RymanSatProject/hobby_sat_book/05_Schematic/esp32/2_top.png

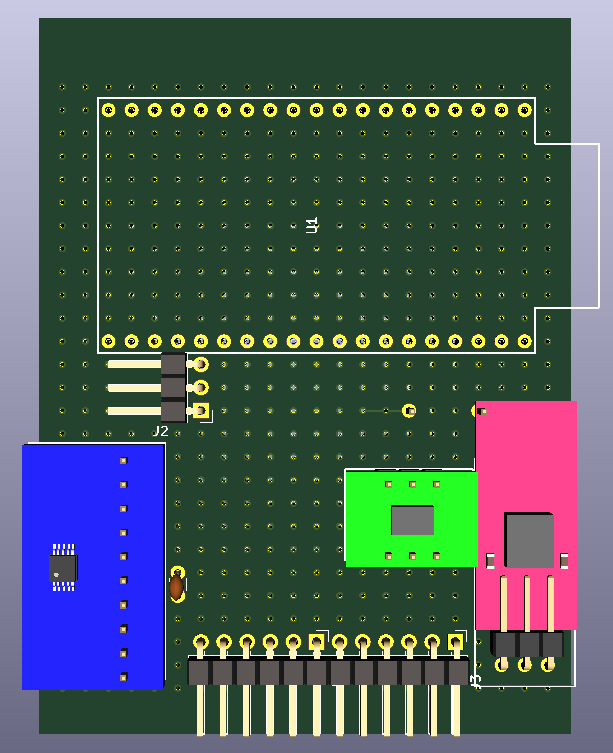
05_Schematic/esp32/2_top.png
