RymanSatProject/hobby_sat_book/05_Schematic/RaspberryPi/3_top.jpg

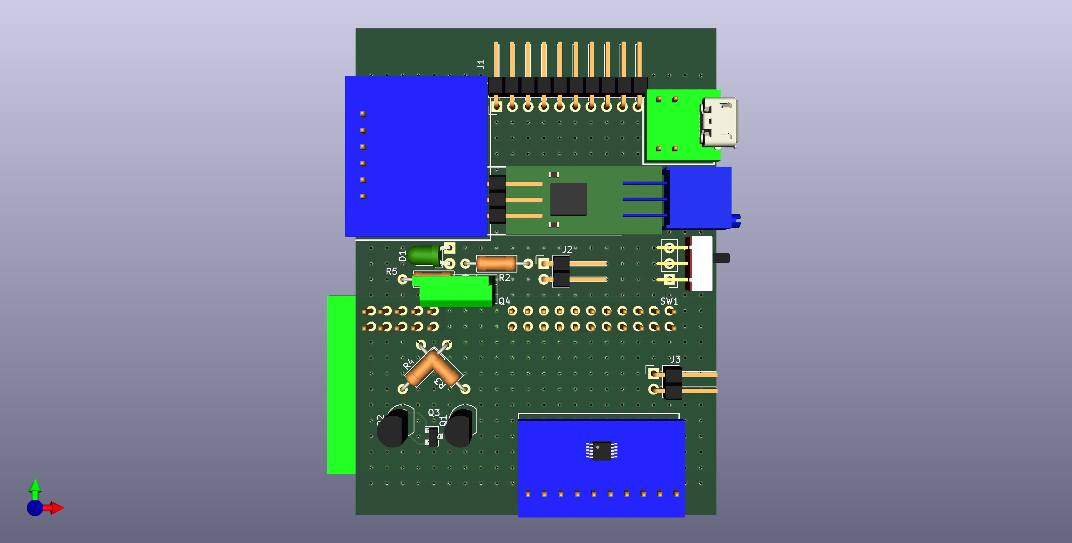
05_Schematic/RaspberryPi/3_top.jpg
