RymanSatProject/hobby_sat_book/05_Schematic/RaspberryPi/USB2.png

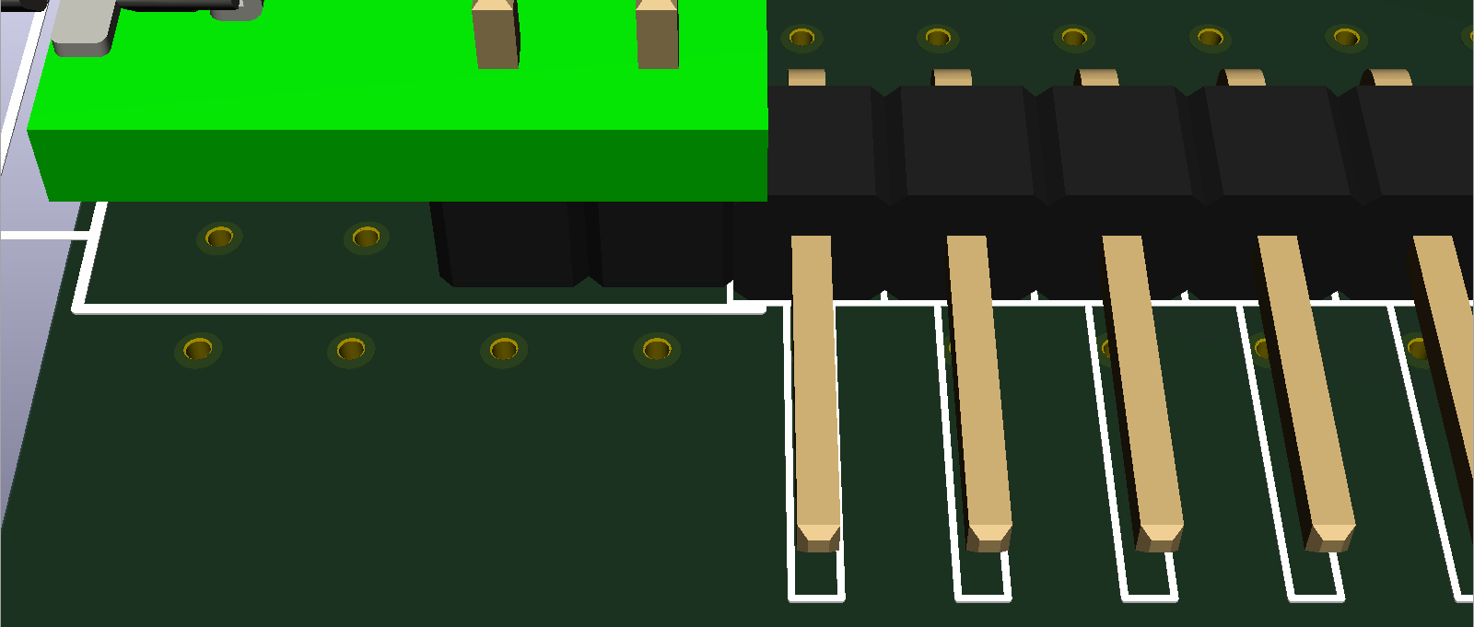
05_Schematic/RaspberryPi/USB2.png
