RymanSatProject/hobby_sat_book/05_Schematic/stm32/1_top.png

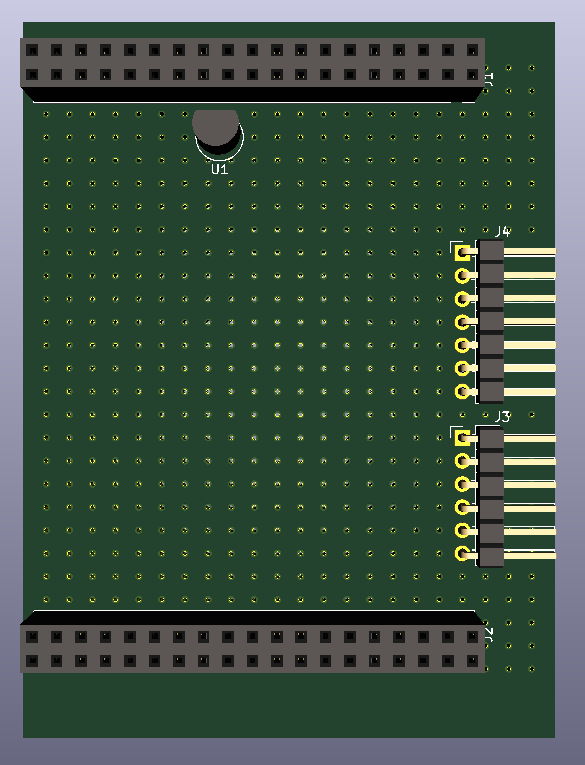
05_Schematic/stm32/1_top.png
