RymanSatProject/hobby_sat_book/10_Ch7_Sup/img/P178_fig66.jpg

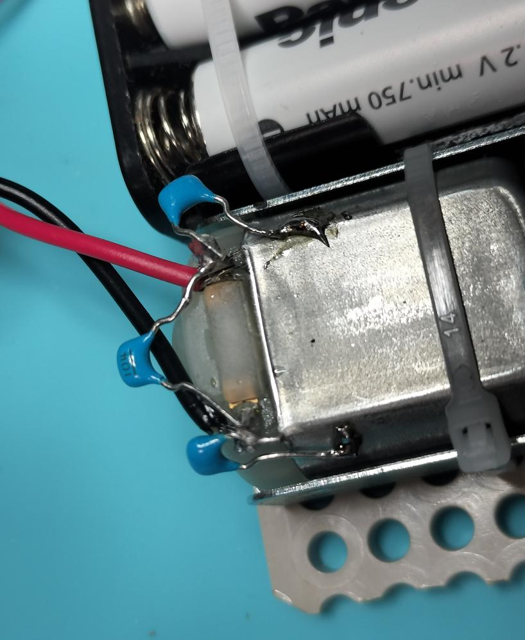
10_Ch7_Sup/img/P178_fig66.jpg
