RymanSatProject/hobby_sat_book/05_Schematic/RaspberryPi/3d/INA219 v1.step

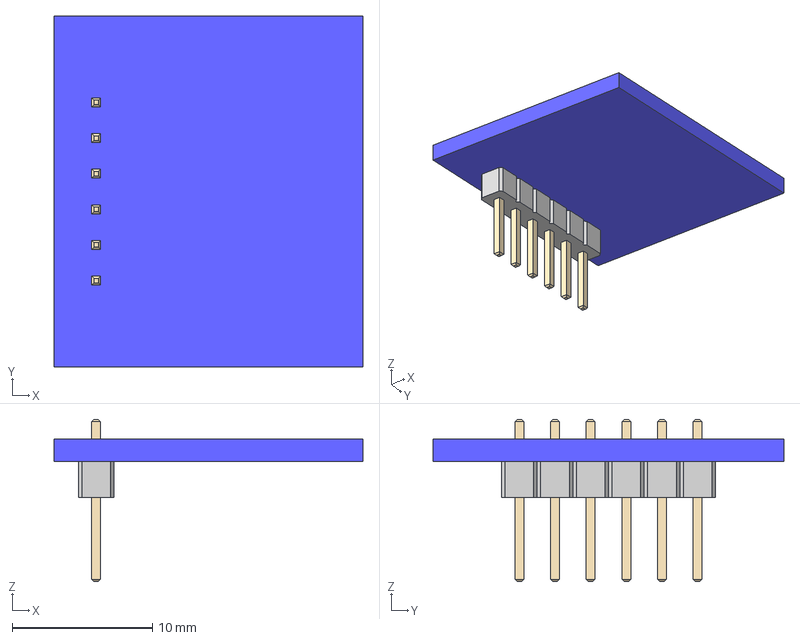
[picture p53: CAD file, 2023-04-15]
05_Schematic/RaspberryPi/3d/INA219 v1.step
22.0 x 25.0 x 11.5 mm
