RymanSatProject/hobby_sat_book/05_Schematic/esp32/3d/PinHeader_1x03_P2.54mm_Horizontal.step

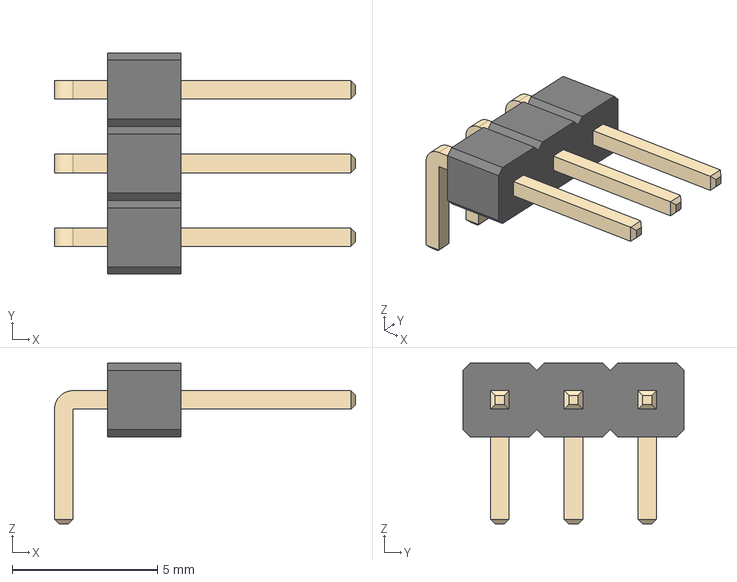
[picture p54: CAD file, 2023-04-15]
05_Schematic/esp32/3d/PinHeader_1x03_P2.54mm_Horizontal.step
10.4 x 7.62 x 5.54 mm
