RymanSatProject/hobby_sat_book/05_Schematic/RaspberryPi/3d/User Library-Mini Slide Switch-3Ppin-SPDT-0_3A.STEP

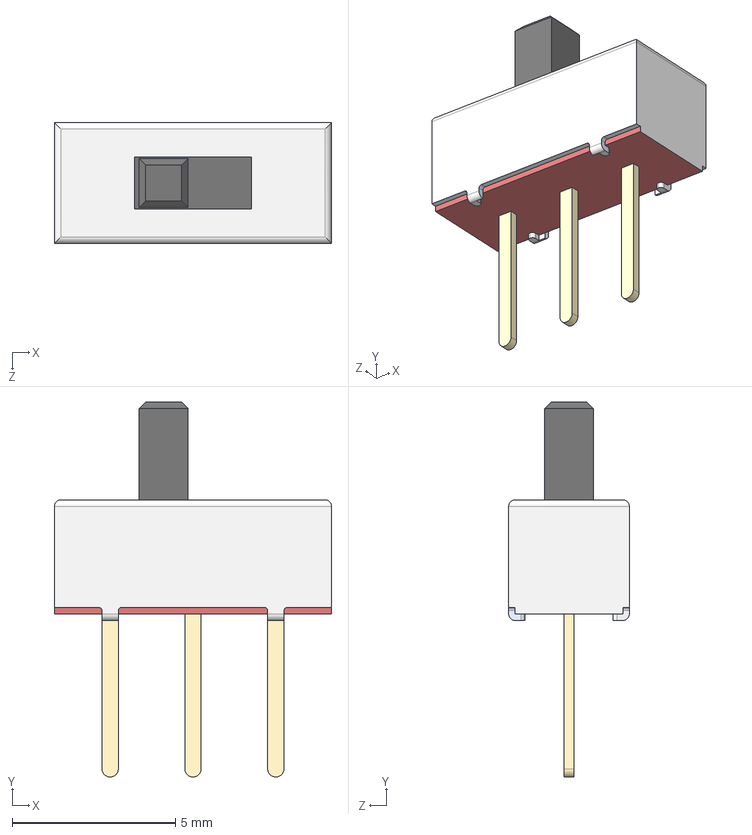
[picture p55: CAD file, 2023-04-15]
05_Schematic/RaspberryPi/3d/User Library-Mini Slide Switch-3Ppin-SPDT-0_3A.STEP
8.50 x 11.5 x 3.70 mm
