RymanSatProject/hobby_sat_book/05_Schematic/esp32/3d/R_1210_3225Metric.step

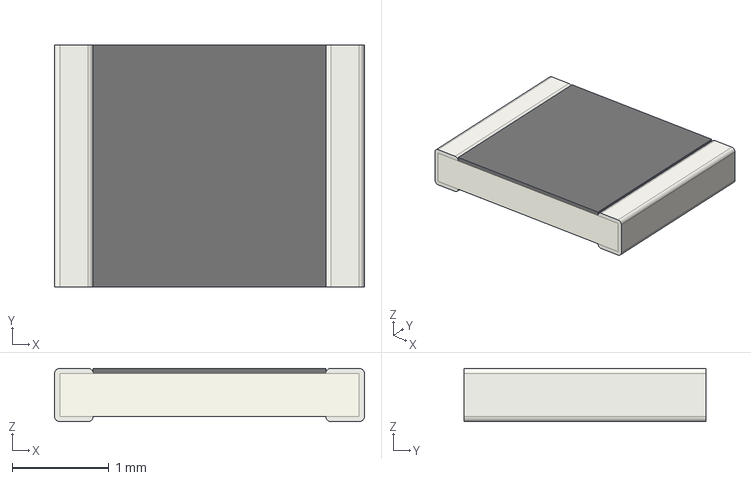
[picture p56: CAD file, 2023-04-15]
05_Schematic/esp32/3d/R_1210_3225Metric.step
3.20 x 2.50 x 0.55 mm
