RymanSatProject/hobby_sat_book/05_Schematic/RaspberryPi/3d/LED_D3.0mm_Horizontal_O1.27mm_Z2.0mm.step

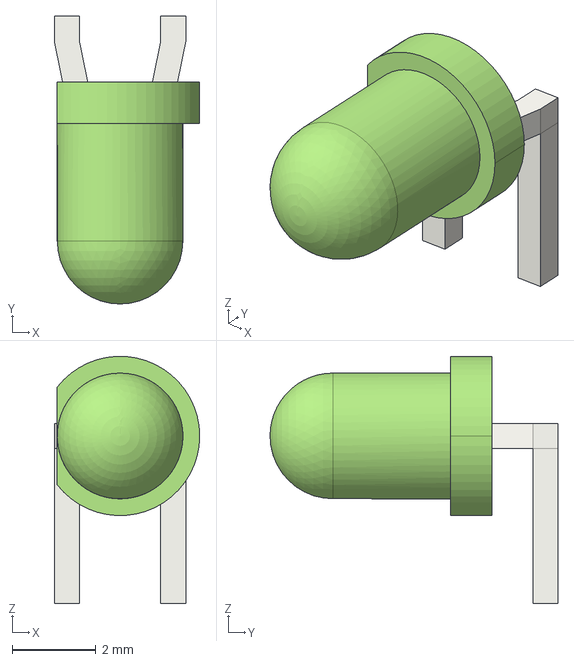
[picture p57: CAD file, 2023-04-15]
05_Schematic/RaspberryPi/3d/LED_D3.0mm_Horizontal_O1.27mm_Z2.0mm.step
3.47 x 6.87 x 5.90 mm
