RymanSatProject/hobby_sat_book/05_Schematic/RaspberryPi/3d/raspi v3.step

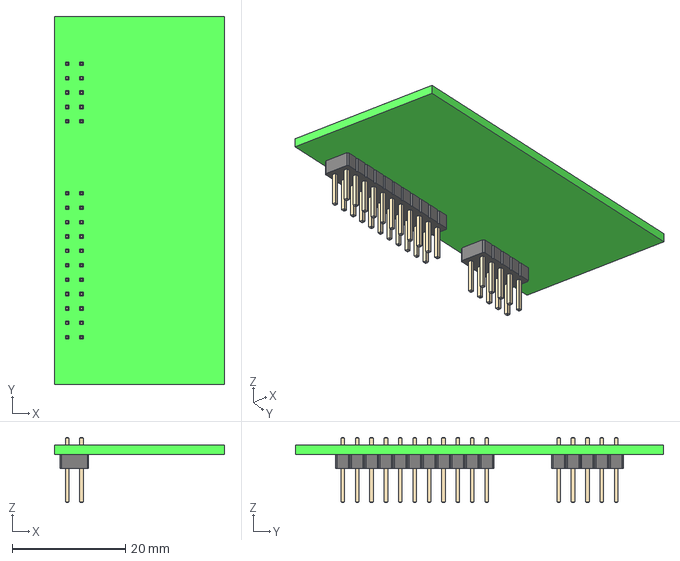
[picture p59: CAD file, 2023-04-15]
05_Schematic/RaspberryPi/3d/raspi v3.step
30.0 x 65.0 x 11.5 mm
PinHeader_2x05_P2.54mm_Vertical
PinHeader_2x11_P2.54mm_Vertical
