RymanSatProject/hobby_sat_book/05_Schematic/RaspberryPi/3d/TO-220-3_Vertical.step

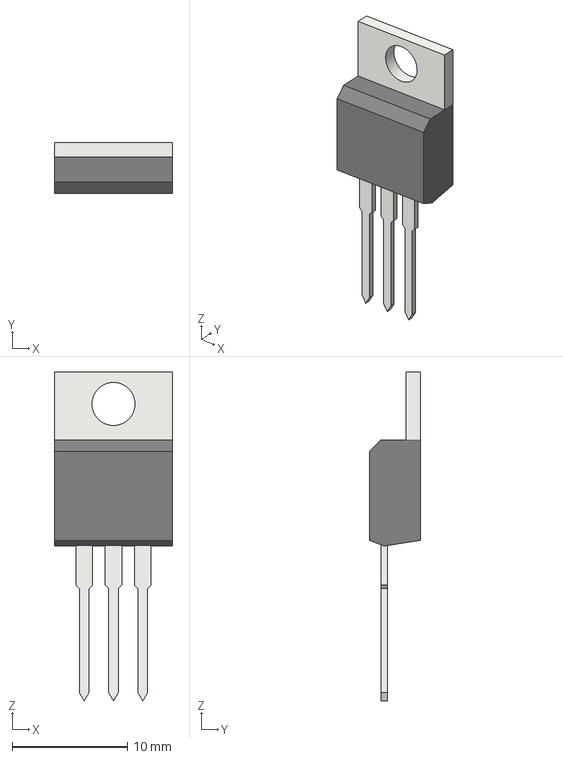
[picture p60: CAD file, 2023-04-15]
05_Schematic/RaspberryPi/3d/TO-220-3_Vertical.step
10.2 x 4.46 x 28.5 mm
