RymanSatProject/hobby_sat_book/05_Schematic/RaspberryPi/3d/USB v3.step

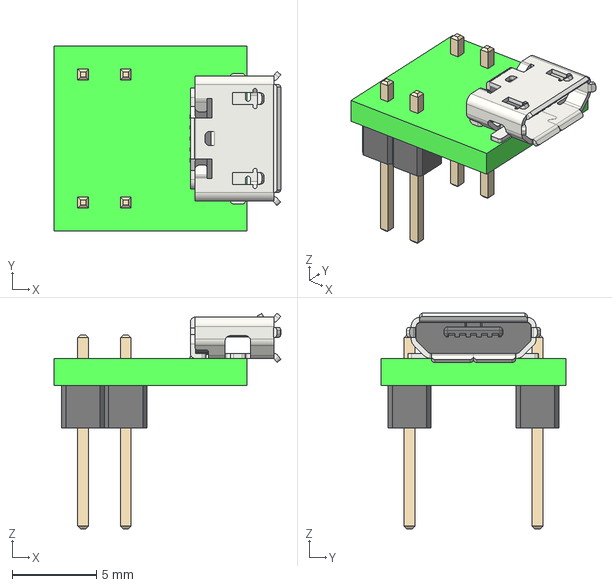
[picture p61: CAD file, 2023-04-15]
05_Schematic/RaspberryPi/3d/USB v3.step
13.5 x 11.0 x 12.8 mm
USB_Micro-B_Molex_47346-0001 v1
PinHeader_1x02_P2.54mm_Vertical x 2
