RymanSatProject/hobby_sat_book/05_Schematic/RaspberryPi/3d/AE-LXDC55-2 v3.step

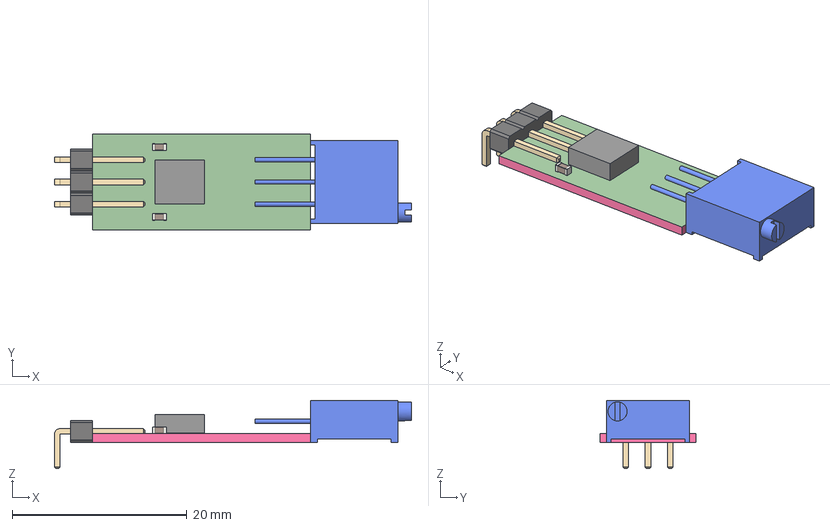
[picture p62: CAD file, 2023-04-15]
05_Schematic/RaspberryPi/3d/AE-LXDC55-2 v3.step
40.9 x 11.0 x 7.83 mm
C_0603_1608Metric x 2
Pins
3296W
