RymanSatProject/hobby_sat_book/00_errata/image/P145_図12.jpg

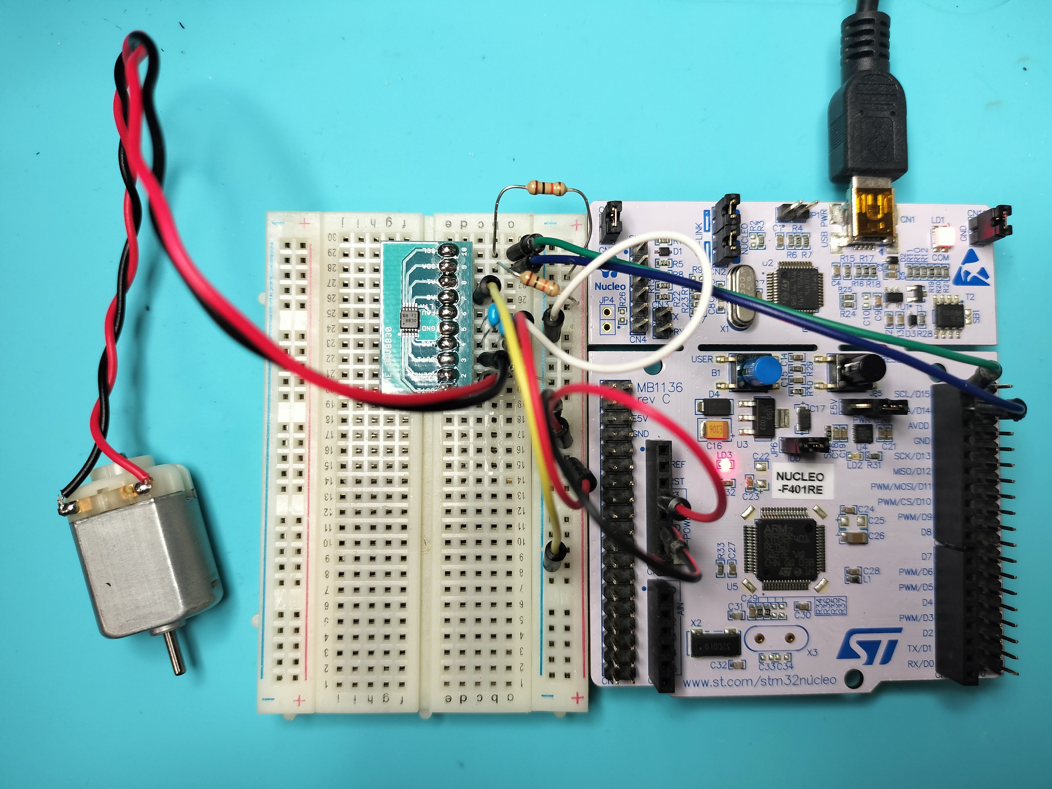
00_errata/image/P145_図12.jpg
