RymanSatProject/hobby_sat_book/00_errata/image/P146_図14.jpg

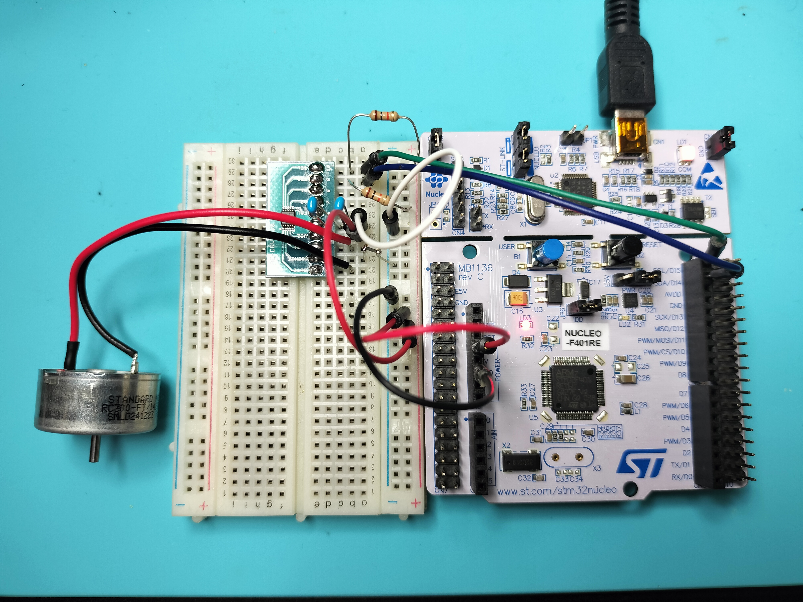
00_errata/image/P146_図14.jpg
