RymanSatProject/hobby_sat_book/00_errata/image/P161_図37.jpg

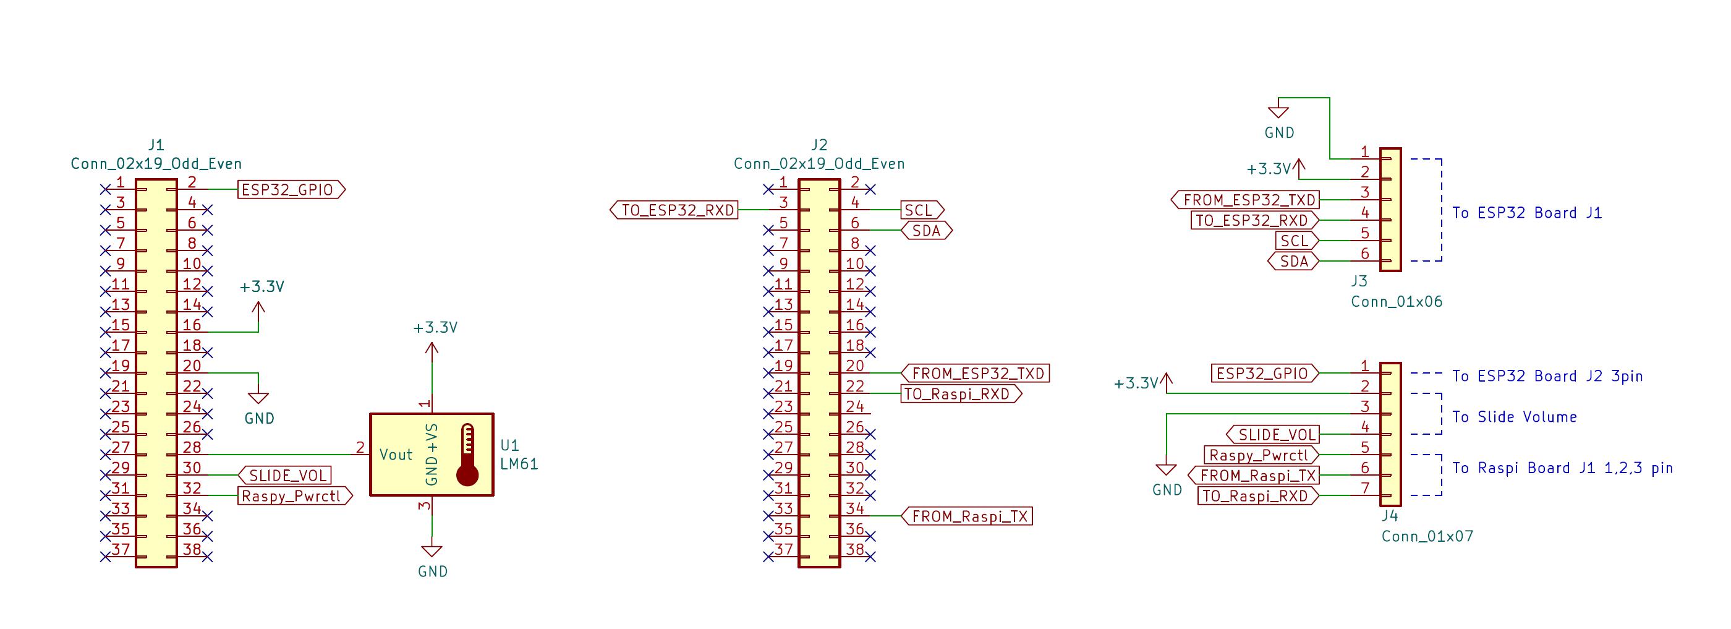
00_errata/image/P161_図37.jpg
