RymanSatProject/hobby_sat_book/00_errata/image/P161_図38.jpg

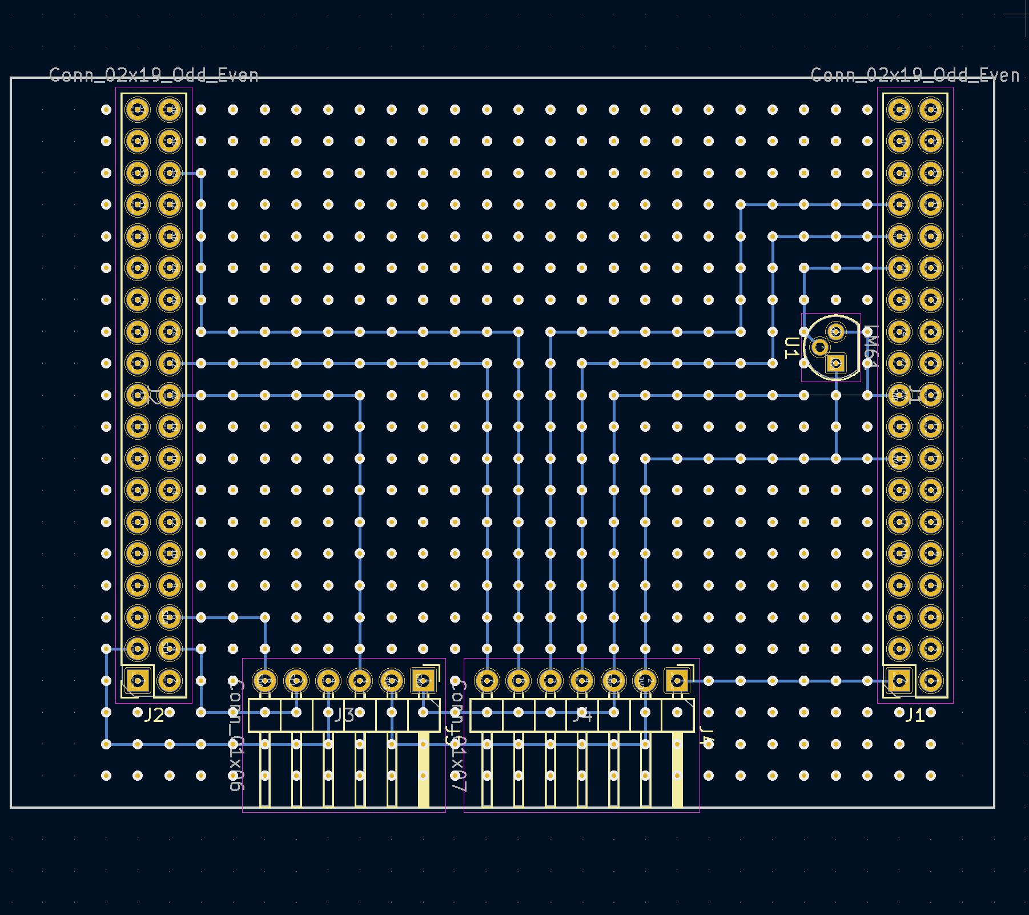
00_errata/image/P161_図38.jpg
