RymanSatProject/hobby_sat_book/00_errata/image/P163_図41.png

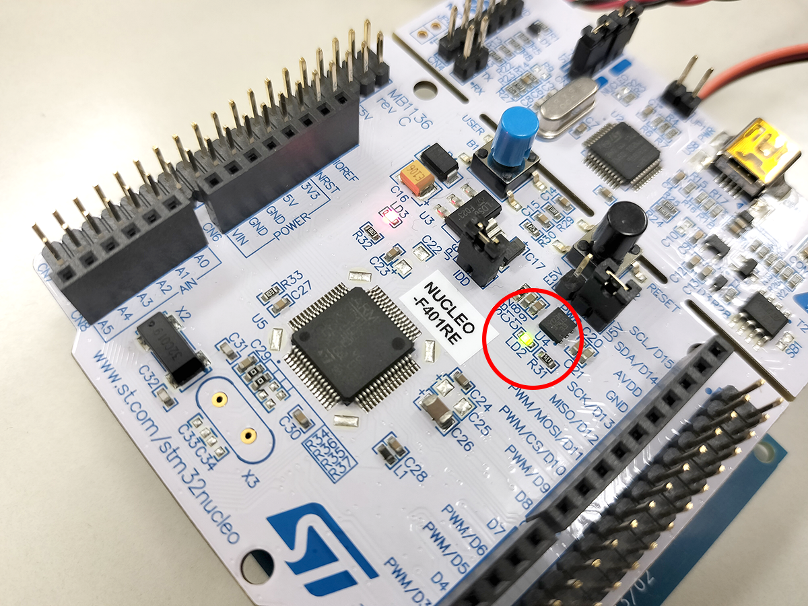
00_errata/image/P163_図41.png
