RymanSatProject/hobby_sat_book/00_errata/image/P168_図51.jpg

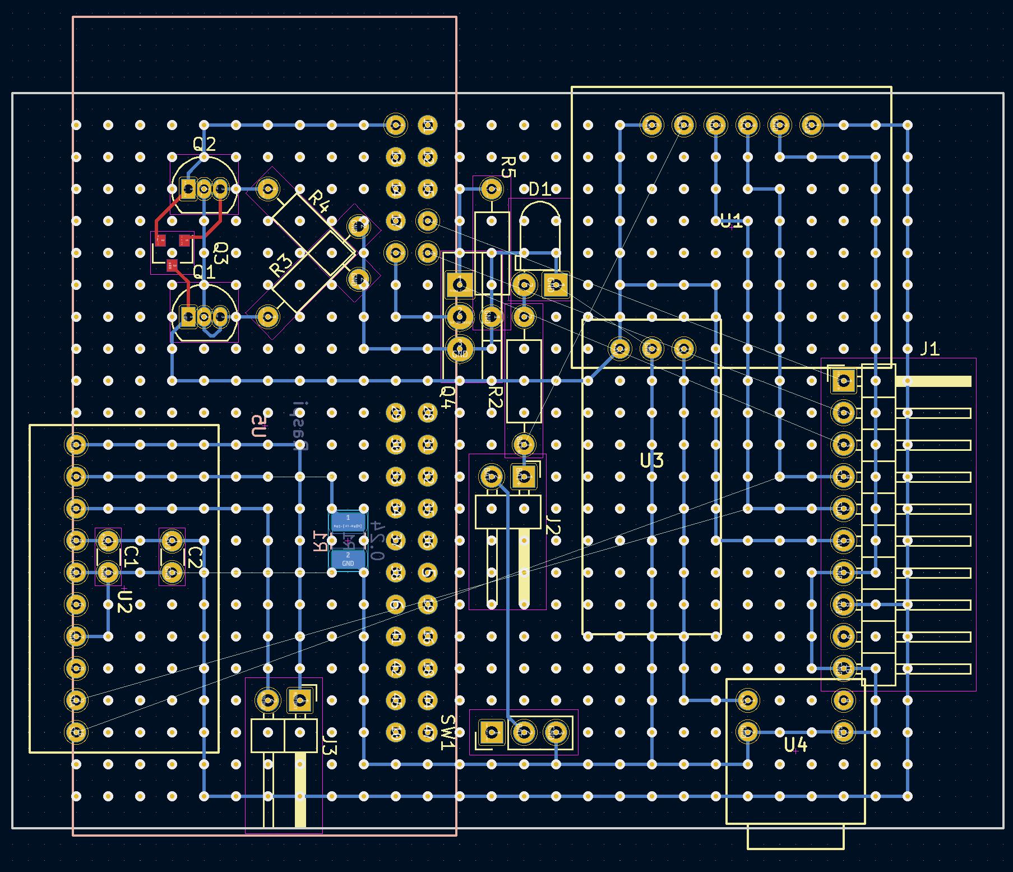
00_errata/image/P168_図51.jpg
